bit-shift-io/bike-aid/mcu-attiny-cpp/schematic.kicad_sch

## KiCad design mcu-attiny-cpp/schematic.kicad_sch (2024-03-28)

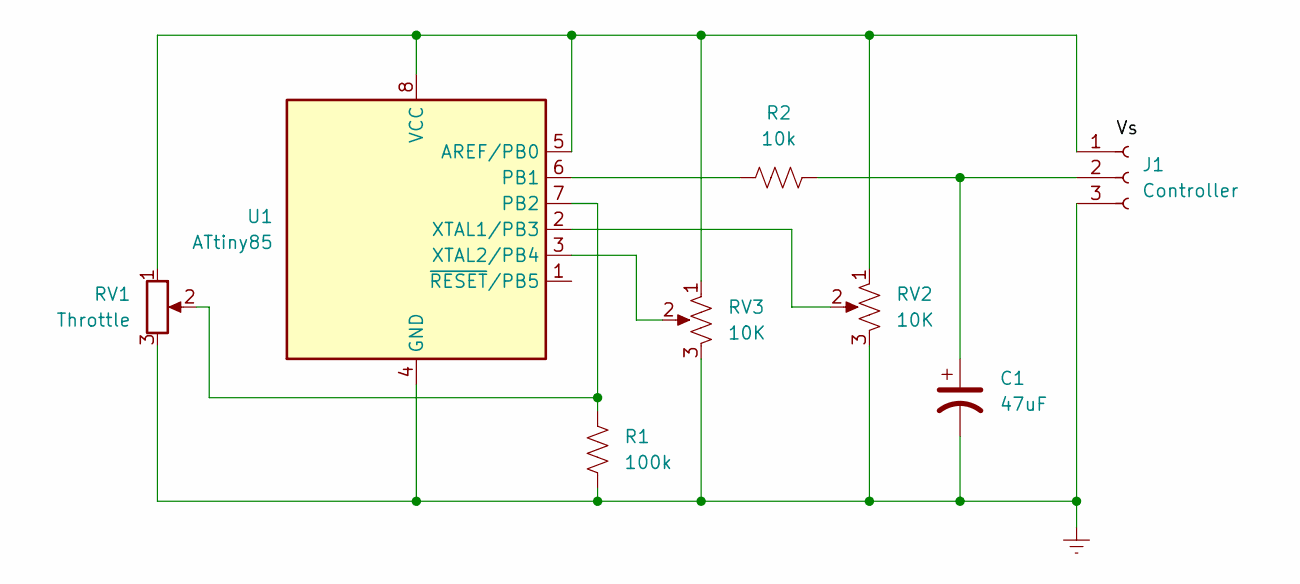
[picture p4: schematic schematic.kicad_sch]

Parts:
C1: 47uF
J1: Controller
R1: 100k
R2: 10k
RV1: Throttle
RV2, RV3: 10K
U1: ATtiny85; DIP-8_W7.62mm

Connections:
Earth: C1.2, J1.3, R1.2, RV1.3, RV2.3, RV3.3, U1.4 (GND)
unnamed: C1.1, J1.2, R2.1
unnamed: J1.1, RV1.1, RV2.1, RV3.1, U1.5 (AREF/PB0), U1.8 (VCC)
unnamed: R1.1, RV1.2, U1.7 (PB2)
unnamed: R2.2, U1.6 (PB1)
unnamed: RV2.2, U1.2 (XTAL1/PB3)
unnamed: RV3.2, U1.3 (XTAL2/PB4)
