bit-shift-io/bike-aid/mcu-esp-cpp/src/main.cpp

/*
  Bike Aid

  This is an ebike tool which does the following:
  - Bluetooth interface
  - Power on/off
  - Lights on/off
  - Battery power meter
  - Alarm system
  - Speedometer
  - Trip Odometer
  - Trip duration
  - Throttle smoothing
  - Throttle limiting / speed limiting
  - Throttle deadband adjustment
  - Temperature

  Bronson Mathews, 2024
*/

/*
Note: if using pins that dont exist the system will crash. Be cautious when setting new classes
*/

#include "Arduino.h"
#include "log.h"
#include "system.h"
#include "store.h"
#include "alarm.h"
#include "clock.h"
#include "throttle.h"
#include "speed.h"
#include "battery.h"
#include "system.h"
#include "power.h"
#include "temperature.h"
#include "bluetooth.h"


void setup() {

  // order important
  Log.init(115200);
  Store.init();
  Bluetooth.init();
  System.init();

  // enable modules
  // testing set true
  Temperature::instance().set_enable(true);
  Alarm::instance().set_enable(true);
  Speed::instance().set_enable(true);
  Throttle::instance().set_enable(false);
  Power::instance().set_enable(true);
  Clock::instance().set_enable(true);

  Log.println("boot ok!");Log.println();
}

void loop() {
  Alarm::instance().update();
  Throttle::instance().update();
  Speed::instance().update();
  Clock::instance().update();
  Temperature::instance().update();
}
