bit-shift-io/bike-aid/mcu-nrf-rs/src/tasks/piezo.rs

use crate::utils::{note::*, melody, signals};
use embassy_nrf::gpio::AnyPin;
use defmt::info;
use embassy_nrf::peripherals::PWM0;
use embassy_nrf::pwm::SimplePwm;
use embassy_time::Timer;

const TASK_ID: &str = "PIEZO";

#[embassy_executor::task]
pub async fn task(
    pwm_device: PWM0,
    pin: AnyPin
) {
    //return; // debug

    info!("{}", TASK_ID);

    let mut pwm = SimplePwm::new_1ch(pwm_device, pin);
    let mut rec_mode = signals::PIEZO_MODE.receiver().unwrap();
    let mut piezo_mode = PiezoMode::None;

    loop {
        // Try to poll read new mode
        // doing this way allows us to use the default mode, if no value is set
        if let Some(b) = rec_mode.try_changed() {piezo_mode = b}

        match piezo_mode {
            PiezoMode::None => {
                pwm.disable();
                piezo_mode = rec_mode.changed().await;
            },
            PiezoMode::Boot => {
                boot(&mut pwm).await;
                piezo_mode = PiezoMode::None;
            }, 
            PiezoMode::PowerOn => {
                power_on(&mut pwm).await;
                piezo_mode = PiezoMode::None;
            },
            PiezoMode::PowerOff => {
                power_off(&mut pwm).await;
                piezo_mode = PiezoMode::None;
            }
            PiezoMode::Warning => {
                warning(&mut pwm).await;
                piezo_mode = PiezoMode::None;
            }
            PiezoMode::Alarm => alarm(&mut pwm).await, // loop
            PiezoMode::SuperMarioBros => {
                play_tune(&mut pwm, melody::SUPER_MARIO_BROS.as_slice(), melody::SUPER_MARIO_BROS_TEMPO).await;
                piezo_mode = PiezoMode::None;
            }
            PiezoMode::Notify => {
                notify(&mut pwm).await;
                piezo_mode = PiezoMode::None;
            },
            PiezoMode::RydeOfTheWalkyries => {
                play_tune(&mut pwm, melody::RYDE_OF_THE_WALKYRIES.as_slice(), melody::RYDE_OF_THE_WALKYRIES_TEMPO).await;
                piezo_mode = PiezoMode::None;
            },
            PiezoMode::BeepShort => {
                beep_short(&mut pwm).await;
                piezo_mode = PiezoMode::None;
            },
            PiezoMode::BeepLong => {
                beep_long(&mut pwm).await;
                piezo_mode = PiezoMode::None;
            },
        };
    }
}


#[allow(dead_code)]
#[derive(Clone,Copy)]
pub enum PiezoMode {
    None,
    Boot,
    PowerOn,
    PowerOff,
    Warning,
    Alarm,
    SuperMarioBros,
    Notify,
    RydeOfTheWalkyries,
    BeepShort,
    BeepLong,
}


async fn beep_short(
    pwm: &mut SimplePwm<'_, PWM0>, // dont need 'static here
) {
    pwm.enable();
    pwm.set_period(NOTE_F6.try_into().unwrap());
    pwm.set_duty(0, pwm.max_duty() / 2); // duty changes with period, so needs to be reset each time
    Timer::after_millis(100).await;
    pwm.disable();
}


async fn beep_long(
    pwm: &mut SimplePwm<'_, PWM0>, // dont need 'static here
) {
    pwm.enable();
    pwm.set_period(NOTE_D3.try_into().unwrap());
    pwm.set_duty(0, pwm.max_duty() / 2); // duty changes with period, so needs to be reset each time
    Timer::after_millis(400).await;
    pwm.disable();
}


async fn notify(
    pwm: &mut SimplePwm<'_, PWM0>, // dont need 'static here
) {
    let tempo: i32 = 120;
    let tune: [isize; 12] = [
        NOTE_C4, 12, NOTE_C5, 12, NOTE_A3, 12, NOTE_A4, 12 ,NOTE_AS3, 12, NOTE_AS4, 12
    ];
    play_tune(pwm, tune.as_slice(), tempo).await;
}


async fn boot(
    pwm: &mut SimplePwm<'_, PWM0>, // dont need 'static here
) {
    play_tune(pwm, melody::STAR_TREK.as_slice(), melody::STAR_TREK_TEMPO).await;
}


async fn power_on(
    pwm: &mut SimplePwm<'_, PWM0>, // dont need 'static here
) {
    play_tune(pwm, melody::NOKIA.as_slice(), melody::NOKIA_TEMPO).await;
}


async fn power_off(
    pwm: &mut SimplePwm<'_, PWM0>, // dont need 'static here
) {
    play_tune(pwm, melody::NOKIA.as_slice(), melody::NOKIA_TEMPO).await;
}


async fn alarm(
    pwm: &mut SimplePwm<'_, PWM0>, // dont need 'static here
) {
    play_tune(pwm, melody::PACMAN.as_slice(), melody::PACMAN_TEMPO).await;
}


async fn warning(
    pwm: &mut SimplePwm<'_, PWM0>,
) {
    play_tune(pwm, melody::STAR_TREK.as_slice(), melody::STAR_TREK_TEMPO).await;
}


async fn play_tune(
    pwm: &mut SimplePwm<'_, PWM0>, 
    tune: &[isize], 
    tempo: i32
) {
    let length = tune.len() / 2;
    let wholenote = (60000.0 * 4.0) / tempo as f32; // wholenote (ms) = 60,000 (1 minute in ms) * 4 (length of whole note) / tempo (bpm)
    let duty = pwm.max_duty() / 2; // piezo driver suggests 50% of max duty


    // loop over each note,duration combo
    for n in (0..=length).step_by(2) {

        // calculates the duration of each note
        let mut duration: f32 = 0.0;
        let divider = tune[n + 1] as i16; // can be negative
        if divider > 0 {
            // regular note, just proceed
            duration = wholenote / divider as f32;
        } else if divider < 0 {
            // dotted notes are represented with negative durations!!
            duration = wholenote / divider.abs() as f32;
            duration *= 1.5 as f32; // increases the duration in half for dotted notes
        }
        let note_duration = (duration * 0.9) as u64;
        let delay_duration = (duration * 0.1) as u64;

        // get the note value
        let note_val = tune[n].try_into().unwrap();
        if note_val != 0 { // 0 is a rest, so no tune
            pwm.enable();
            pwm.set_period(note_val); // TODO: try 16_000_000 / tone.1
            pwm.set_duty(0, duty); // duty changes with period, so needs to be reset each time
        }

        // Wait for the specief duration before playing the next note.
        // we only play the note for 90% of the duration, leaving 10% as a pause
        Timer::after_millis(note_duration).await;

        // stop the waveform generation before the next note.
        pwm.disable();
        Timer::after_millis(delay_duration).await;
    }
}
