bit-shift-io/bike-aid/mcu-nrf-rs/src/tasks/cruise.rs

use core::future;

use crate::utils::{settings, signals};
use defmt::info;
use embassy_futures::select::{select, select3, Either3};
use embassy_time::Instant;

const TASK_ID: &str = "CRUISE";
const NO_THROTTLE_THRESHOLD: u16 = 1200;
const FULL_THROTTLE_THRESHOLD: u16 = 2600;
const BRAKE_TAP_TIME: u64 = 300; // ms
const THROTTLE_MAX_COUNT: u8 = 8; // this equals X x 100ms of throttle updates

#[embassy_executor::task]
pub async fn task() {
    info!("{}", TASK_ID);

    // power on/off
    let mut rec_power_on = signals::POWER_ON.receiver().unwrap();
    let mut state_power_on = rec_power_on.try_get().unwrap();

    // sport mode - cruise enabled/disabled
    let mut rec_sport_mode_on = signals::SPORT_MODE_ON.receiver().unwrap();
    let mut state_sport_mode_on = rec_sport_mode_on.try_get().unwrap();

    loop {
        match select3(rec_power_on.changed(), rec_sport_mode_on.changed(), run(state_power_on, state_sport_mode_on)).await {
            Either3::First(b) => { state_power_on = b; },
            Either3::Second(b) => { state_sport_mode_on = b; },
            Either3::Third(_) => {}
        }
    }
}


async fn run(power_on: bool, sport_mode_on: bool) {
    // power off/sport mode
    // throttle and brake dont work when power off
    // but we need to reset it when powered off purely for gui
    if !power_on || sport_mode_on {
        set_cruise(0).await; 
        future::pending().await // wait/yield forever doing nothing
    }

    // throttle and brake tap detection
    select(throttle_tap(), brake_tap()).await;
}

async fn brake_tap() {
    let mut rec_brake_on = signals::BRAKE_ON.receiver().unwrap();

     // wait for brake off - not sure if this is needed?
     //rec_brake_on.changed_and(|b| *b == false).await;

    loop {
        // brake should be off here from boot & previous loop
        // wait for brake on
        rec_brake_on.changed_and(|b| *b == true).await;

        // start timing
        let time = Instant::now();

        // wait for brake off
        rec_brake_on.changed_and(|b| *b == false).await;

        if delta(time) < BRAKE_TAP_TIME {
            //info!("brake tap");
            decrement_cruise().await;
        } else {
            // regaulr brake, so reset cruise
            set_cruise(0).await;
        }
    }
}


async fn throttle_tap() {
    let mut rec_throttle = signals::THROTTLE_IN.receiver().unwrap();
    let mut throttle_voltage = rec_throttle.changed().await; // millivolts, initial value

    loop {
        // Wait for throttle to go below the NO_THROTTLE_THRESHOLD - throttle off
        while throttle_voltage > NO_THROTTLE_THRESHOLD {
            throttle_voltage = rec_throttle.changed().await;
        }

        // Wait for the throttle to exceed the NO_THROTTLE_THRESHOLD - throttle start/low
        while throttle_voltage < NO_THROTTLE_THRESHOLD {
            throttle_voltage = rec_throttle.changed().await;
        }

        // start timing, each update is 100ms
        let mut count = 0;

        // Wait for the throttle to exceed the FULL_THROTTLE_THRESHOLD - throttle high
        while throttle_voltage < FULL_THROTTLE_THRESHOLD && count < THROTTLE_MAX_COUNT {
            throttle_voltage = rec_throttle.changed().await;
            count += 1;
        }

        // Now we are at full throttle, wait for it to drop below the NO_THROTTLE_THRESHOLD - throttle off
        while throttle_voltage > NO_THROTTLE_THRESHOLD && count < THROTTLE_MAX_COUNT {
            throttle_voltage = rec_throttle.changed().await;
            count += 1;
        }

        // Check if the tap was detected within the time limit
        if count < THROTTLE_MAX_COUNT {
            //info!("tap detected");
            increment_cruise().await;
        }
    }
}


pub fn delta(t: Instant) -> u64 {
    Instant::now().duration_since(t).as_millis()
}


async fn increment_cruise() {
    let mut level = signals::CRUISE_LEVEL.try_get().unwrap();
    if level == 5 { return; }

    level += 1;
    // wrap around 0-4, move 0 -> 5 = range 1-5 instead of 0-4
    //level = (level + 1) % 5; 
    //if level == 0 { level = 5; }

    set_cruise(level).await;
}


async fn decrement_cruise() {
    let mut level = signals::CRUISE_LEVEL.try_get().unwrap();
    if level == 0 { return; }

    level -= 1;
    // wrap around 0-4, move 5 -> 0 = range 1-5 instead of 0-4
    //level = (level - 1) % 5;
    //if level == 0 { level = 5; }

    set_cruise(level).await;
}


async fn set_cruise(level: u8) {
    let current_level = signals::CRUISE_LEVEL.try_get().unwrap();

    // only send if changed
    if current_level != level {
        // set voltage
        let cruise_voltages = *settings::CRUISE_VOLTAGES.lock().await;
        let voltage = if level == 0 { 0 } else { cruise_voltages[(level -1) as usize] }; 
        settings::CRUISE_VOLTAGE.dyn_sender().send(voltage);

        // set level
        signals::CRUISE_LEVEL.dyn_sender().send(level);
        signals::send_ble(signals::BleHandles::CruiseLevel, &[level]);
    
        // beep
        let send_piezo = signals::PIEZO_MODE.sender();
        send_piezo.send(signals::PiezoModeType::BeepShort);
    }
}
