bit-shift-io/bike-aid/mcu-nrf-rs/src/tasks/bluetooth.rs

use crate::ble::server::{self, Server};
use defmt::*;
use embassy_executor::Spawner;
use embassy_futures::select::select;
use core::mem;
use nrf_softdevice::ble::advertisement_builder::{Flag, LegacyAdvertisementBuilder, LegacyAdvertisementPayload, ServiceList};
use nrf_softdevice::ble::{self, gatt_server, peripheral, Connection};
use nrf_softdevice::{raw, Softdevice};
use core::pin::pin;

const TASK_ID: &str = "BLUETOOTH";

// main task
#[embassy_executor::task]
pub async fn task(
    spawner: Spawner
) {
    info!("{}", TASK_ID);
    
    // start softdevice with fixed address
    let softdevice = Softdevice::enable(&get_config());
    let address = ble::Address::new(ble::AddressType::Public, [0x45, 0x42, 0x60, 0xFB, 0xEB, 0xD7]);
    ble::set_address(softdevice, &address);
    let server: Server = unwrap!(Server::new(softdevice));
    spawner.must_spawn(softdevice_task(softdevice));
   
    // advertise and scan data
    static ADV_DATA: LegacyAdvertisementPayload = LegacyAdvertisementBuilder::new()
        .flags(&[Flag::GeneralDiscovery, Flag::LE_Only])
        //.services_16(ServiceList::Incomplete, &[ServiceUuid16::from_u16(0xFE2C)]) // fast pair
        .short_name("BScooter")
        .build();

    static SCAN_DATA: LegacyAdvertisementPayload = LegacyAdvertisementBuilder::new()
        //.services_16(ServiceList::Incomplete, &[ServiceUuid16::from_u16(0xFE2C)]) // fast pair
        .services_128(ServiceList::Incomplete, &[[0x9E, 0xCA, 0xDC, 0x24, 0x0E, 0xE5, 0xA9, 0xE0, 0x93, 0xF3, 0xA3, 0xB5, 0x01, 0x00, 0x40, 0x6E]]) // UART Service
        .build();

    // start the show
    loop {
        let config = peripheral::Config::default();
        let advertisement = peripheral::ConnectableAdvertisement::ScannableUndirected { adv_data: &ADV_DATA, scan_data: &SCAN_DATA };
        let connection: Connection = unwrap!(peripheral::advertise_connectable(softdevice, advertisement, &config).await);

        // Create two futures. Pin locks the memory to the stack
        let server_future = pin!(server::run(&connection, &server));
        let gatt_future = pin!(gatt_server::run(&connection, &server, |_| {})); // no events rigistered

        //  - we only gather data when a client is connected, therefore saving some power.
        //  - when the GATT server finishes operating, our run function does also
        select(server_future, gatt_future).await;

        // disconnect message
        server::disconnected(&connection, &server).await;
    }
}


fn get_config() -> nrf_softdevice::Config {
    nrf_softdevice::Config {
        clock: Some(raw::nrf_clock_lf_cfg_t {
            source: raw::NRF_CLOCK_LF_SRC_RC as u8,
            rc_ctiv: 16,
            rc_temp_ctiv: 2,
            accuracy: raw::NRF_CLOCK_LF_ACCURACY_500_PPM as u8,
        }),
        conn_gap: Some(raw::ble_gap_conn_cfg_t {
            conn_count: 2, // 6
            event_length: 24, // 24
        }),
        conn_gatt: Some(raw::ble_gatt_conn_cfg_t { att_mtu: 517 }), // 517 is the android default
        gatts_attr_tab_size: Some(raw::ble_gatts_cfg_attr_tab_size_t { attr_tab_size: 2048 }), // increase if nomem error, default: attr_tab_size: raw::BLE_GATTS_ATTR_TAB_SIZE_DEFAULT,
        gap_role_count: Some(raw::ble_gap_cfg_role_count_t {
            adv_set_count: 1,
            periph_role_count: 1, // 3
            central_role_count: 1, // 3
            central_sec_count: 0,
            _bitfield_1: raw::ble_gap_cfg_role_count_t::new_bitfield_1(0),
        }),
        gap_device_name: Some(raw::ble_gap_cfg_device_name_t {
            p_value: b"BScooter" as *const u8 as _, // TODO: use device name here
            current_len: 8,
            max_len: 8,
            write_perm: unsafe { mem::zeroed() },
            _bitfield_1: raw::ble_gap_cfg_device_name_t::new_bitfield_1(raw::BLE_GATTS_VLOC_STACK as u8),
        }),
        ..Default::default()
    }
}


// softdevice task
#[embassy_executor::task]
async fn softdevice_task(sd: &'static Softdevice) {
    sd.run().await;
}
