bit-shift-io/bike-aid/mcu-nrf-rs/src/tasks/clock.rs

use crate::utils::signals;
use embassy_futures::select::select;
use embassy_time::{Instant, Timer};
use defmt::info;

const TASK_ID: &str = "CLOCK";

#[embassy_executor::task]
pub async fn task() {
    info!("{}", TASK_ID);

    // power on/off
    let mut rec_power_on = signals::POWER_ON.receiver().unwrap();

    loop { 
        if rec_power_on.changed().await {
            select(rec_power_on.changed(), clock()).await;
        }
    }
}


async fn clock() {
    let mut last_minutes: u8 = 0;
    let mut last_hours: u8 = 0;
    let start_time = Instant::now();

    // send/reset initial time
    signals::send_ble(signals::BleHandles::ClockMinutes, &[0]);
    signals::send_ble(signals::BleHandles::ClockHours, &[0]);
    
    loop {
        Timer::after_secs(60).await;

        let seconds = start_time.elapsed().as_secs();
        let hours = ((seconds % 86400) / 3600) as u8; // 3600 seconds in an hour
        let minutes = ((seconds % 3600) / 60) as u8; // 60 seconds in a minute

        if minutes != last_minutes {
            last_minutes = minutes;
            signals::send_ble(signals::BleHandles::ClockMinutes, &[minutes]);
        };
    
        if hours != last_hours {
            last_hours = hours;
            signals::send_ble(signals::BleHandles::ClockHours, &[hours]);
        }
    }
}
