bit-shift-io/bike-aid/mcu-nrf-rs/src/tasks/mod.rs

pub mod alarm;
pub mod battery_adc;
pub mod battery;
pub mod bluetooth;
pub mod brake;
pub mod cli;
pub mod clock;
pub mod cruise;
pub mod gyroscope;
pub mod led;
pub mod manual_override;
pub mod park_brake;
pub mod piezo;
pub mod power_down;
pub mod rtt;
pub mod speed;
pub mod switch_power;
pub mod temperature;
pub mod throttle_adc;
pub mod throttle_dac;
pub mod throttle;
