bit-shift-io/bike-aid/mcu-esp-cpp/include/bluetooth.h

// handy guide https://github.com/nkolban/ESP32_BLE_Arduino/blob/master/examples/BLE_uart/BLE_uart.ino

#pragma once
#include "NimBLEDevice.h"


class BluetoothClass {

  public:
    BluetoothClass();
    void init();

    void set_value(BLECharacteristic *pCharacteristic, std::string value);
    void set_value(BLECharacteristic *pCharacteristic, uint8_t value);

    // callbacks
    void on_connect(BLEServer* pServer);
    void on_disconnect(BLEServer* pServer);
    void on_write(BLECharacteristic *pCharacteristic);


    // services

    // characteristics
    BLECharacteristic *power_system_characteristic;
    BLECharacteristic *power_lights_characteristic;
    BLECharacteristic *alarm_enabled_characteristic;
    BLECharacteristic *battery_level_characteristic;
    BLECharacteristic *throttle_smoothing_characteristic;
    BLECharacteristic *temperature_characteristic;
    BLECharacteristic *trip_distance_characteristic;
    BLECharacteristic *trip_duration_characteristic;
    BLECharacteristic *speed_characteristic;

    // uart
    BLECharacteristic *uart_tx_characteristic;
    BLECharacteristic *uart_rx_characteristic;

  private:
    // https://www.uuidgenerator.net/
    const char* SERVICE_UUID = "8fabcc8a-0a6e-4c37-b640-eb5adf88b465";
    const char* THROTTLE_SMOOTHING_UUID = "beb5483e-36e1-0000-b7f5-ea07361b26a8";
    const char* ALARM_ENABLED_UUID = "beb5483e-36e1-0001-b7f5-ea07361b26a8";
    const char* POWER_SYSTEM_UUID = "beb5483e-36e1-0002-b7f5-ea07361b26a8";
    const char* POWER_LIGHTS_UUID = "beb5483e-36e1-0003-b7f5-ea07361b26a8";

    const int PIN_CODE = 123456;

    // UART service UUID
    // https://learn.adafruit.com/introducing-adafruit-ble-BluetoothClass-low-energy-friend/uart-service
    const char* SERVICE_UART_UUID =       "6E400001-B5A3-F393-E0A9-E50E24DCCA9E"; 
    const char* CHARACTERISTIC_RX_UUID =  "6E400002-B5A3-F393-E0A9-E50E24DCCA9E"; // tx??
    const char* CHARACTERISTIC_TX_UUID =  "6E400003-B5A3-F393-E0A9-E50E24DCCA9E"; // rx id??

    // server
    BLEServer *pServer = NULL;



    // callbacks
    bool device_connected = false;
    bool old_device_connected = false;

    // Delay between loops in ms
    const int INTERVAL = 6000; // 1 minute
    unsigned long last_interval = 0;
};

extern BluetoothClass Bluetooth;
