bit-shift-io/bike-aid/mcu-esp-cpp/include/system.h

#pragma once

// guide 
// https://mischianti.org/esp32-practical-power-saving-manage-wifi-and-cpu-1/

class SystemClass {
  
  public:
    SystemClass();
    void init();
    void set_power_low();
    void set_power_high();
    void print_cpu_info();
    void update();
};

extern SystemClass System;
