bit-shift-io/bike-aid/mcu-esp-cpp/src/system.cpp

#include "system.h"
#include <WiFi.h>
#include <esp_wifi.h>
#include "driver/adc.h"
#include <esp_task_wdt.h>
#include "esp32-hal.h"
#include "log.h"

SystemClass System;


SystemClass::SystemClass() {
}


void SystemClass::init() {
  Log.println("SystemClass init");
  print_cpu_info();
  //set_power_low(); // crash!
}


void SystemClass::print_cpu_info() {
  Log.println("-------------");
  Log.print("CPU Freq = ");
  Log.print(getCpuFrequencyMhz());
  Log.println(" MHz");

  Log.print("XTAL Freq = ");
  Log.print(getXtalFrequencyMhz());
  Log.println(" MHz");

  Log.print("APB Freq = ");
  Log.print(getApbFrequency());
  Log.println(" Hz");
  Log.println("-------------");
}


void SystemClass::set_power_low() {
  // wifi power mode
  //esp_wifi_set_ps(WIFI_PS_MAX_MODEM); // lowest
  //esp_wifi_set_ps(WIFI_PS_MIN_MODEM); // low

  // disable adc and wifi
  adc_power_off();
  WiFi.disconnect(true);  // Disconnect from the network
  WiFi.mode(WIFI_OFF);    // Switch WiFi off

  // bluetooth off
  //btStop();

  // cpu freq, bluetooth needs 80mhz or above
  //  240, 160, 80    <<< For all XTAL types
  //  40, 20, 10      <<< For 40MHz XTAL
  //  26, 13          <<< For 26MHz XTAL
  //  24, 12          <<< For 24MHz XTAL
  setCpuFrequencyMhz(80);

  // disable watch dog when using less than 80mhz
  //disableCore0WDT();
}


void SystemClass::set_power_high() {
  // wifi power mode
  esp_wifi_set_ps(WIFI_PS_NONE); // default

  // enable adc and wifi
  adc_power_on(); delay(200);
  WiFi.disconnect(false);  // Reconnect the network
  WiFi.mode(WIFI_STA);    // Switch WiFi off

  // bluetooth on
  btStart();

  // cpu freq
  setCpuFrequencyMhz(240);
}
