bit-shift-io/bike-aid/mcu-nrf-rs/src/utils/note.rs

#![allow(dead_code)]

// note frequency chart https://muted.io/note-frequencies/
// needs to be isize(not usize) because durations can be negative

pub const REST: isize = 0;
pub const NOTE_C0: isize = 16;
pub const NOTE_CS0: isize = 17;
pub const NOTE_D0: isize = 19;
pub const NOTE_DS0: isize = 21;
pub const NOTE_E0: isize = 22;
pub const NOTE_F0: isize = 24;
pub const NOTE_FS0: isize = 26;
pub const NOTE_G0: isize = 28;
pub const NOTE_GS0: isize = 29;
pub const NOTE_A0: isize = 30;
pub const NOTE_B0: isize = 31;
pub const NOTE_C1: isize = 33;
pub const NOTE_CS1: isize = 35;
pub const NOTE_D1: isize = 37;
pub const NOTE_DS1: isize = 39;
pub const NOTE_E1: isize = 41;
pub const NOTE_F1: isize = 44;
pub const NOTE_FS1: isize = 46;
pub const NOTE_G1: isize = 49;
pub const NOTE_GS1: isize = 52;
pub const NOTE_A1: isize = 55;
pub const NOTE_AS1: isize = 58;
pub const NOTE_B1: isize = 62;
pub const NOTE_C2: isize = 65;
pub const NOTE_CS2: isize = 69;
pub const NOTE_D2: isize = 73;
pub const NOTE_DS2: isize = 78;
pub const NOTE_E2: isize = 82;
pub const NOTE_F2: isize = 87;
pub const NOTE_FS2: isize = 93;
pub const NOTE_G2: isize = 98;
pub const NOTE_GS2: isize = 104;
pub const NOTE_A2: isize = 110;
pub const NOTE_AS2: isize = 117;
pub const NOTE_B2: isize = 123;
pub const NOTE_C3: isize = 131;
pub const NOTE_CS3: isize = 139;
pub const NOTE_D3: isize = 147;
pub const NOTE_DS3: isize = 156;
pub const NOTE_E3: isize = 165;
pub const NOTE_F3: isize = 175;
pub const NOTE_FS3: isize = 185;
pub const NOTE_G3: isize = 196;
pub const NOTE_GS3: isize = 208;
pub const NOTE_A3: isize = 220;
pub const NOTE_AS3: isize = 233;
pub const NOTE_B3: isize = 247;
pub const NOTE_C4: isize = 262;
pub const NOTE_CS4: isize = 277;
pub const NOTE_D4: isize = 294;
pub const NOTE_DS4: isize = 311;
pub const NOTE_E4: isize = 330;
pub const NOTE_F4: isize = 349;
pub const NOTE_FS4: isize = 370;
pub const NOTE_G4: isize = 392;
pub const NOTE_GS4: isize = 415;
pub const NOTE_A4: isize = 440;
pub const NOTE_AS4: isize = 466;
pub const NOTE_B4: isize = 494;
pub const NOTE_C5: isize = 523;
pub const NOTE_CS5: isize = 554;
pub const NOTE_D5: isize = 587;
pub const NOTE_DS5: isize = 622;
pub const NOTE_E5: isize = 659;
pub const NOTE_F5: isize = 698;
pub const NOTE_FS5: isize = 740;
pub const NOTE_G5: isize = 784;
pub const NOTE_GS5: isize = 831;
pub const NOTE_A5: isize = 880;
pub const NOTE_AS5: isize = 932;
pub const NOTE_B5: isize = 988;
pub const NOTE_C6: isize = 1047;
pub const NOTE_CS6: isize = 1109;
pub const NOTE_D6: isize = 1175;
pub const NOTE_DS6: isize = 1245;
pub const NOTE_E6: isize = 1319;
pub const NOTE_F6: isize = 1397;
pub const NOTE_FS6: isize = 1480;
pub const NOTE_G6: isize = 1568;
pub const NOTE_GS6: isize = 1661;
pub const NOTE_A6: isize = 1760;
pub const NOTE_AS6: isize = 1865;
pub const NOTE_B6: isize = 1976;
pub const NOTE_C7: isize = 2093;
pub const NOTE_CS7: isize = 2217;
pub const NOTE_D7: isize = 2349;
pub const NOTE_DS7: isize = 2489;
pub const NOTE_E7: isize = 2637;
pub const NOTE_F7: isize = 2794;
pub const NOTE_FS7: isize = 2960;
pub const NOTE_G7: isize = 3136;
pub const NOTE_GS7: isize = 3322;
pub const NOTE_A7: isize = 3520;
pub const NOTE_AS7: isize = 3729;
pub const NOTE_B7: isize = 3951;
pub const NOTE_C8: isize = 4186;
pub const NOTE_CS8: isize = 4435;
pub const NOTE_D8: isize = 4699;
pub const NOTE_DS8: isize = 4978;
pub const NOTE_E8: isize = 5274;
pub const NOTE_F8: isize = 5587;
pub const NOTE_FS8: isize = 5919;
pub const NOTE_G8: isize = 6271;
pub const NOTE_GS8: isize = 6643;
pub const NOTE_A8: isize = 7040;
pub const NOTE_AS8: isize = 7459;
pub const NOTE_B8: isize = 7902;
