bit-shift-io/bike-aid/mcu-nrf-rs/src/utils/mod.rs

pub mod data_slice;
pub mod functions;
pub mod globals;
//pub mod log;
pub mod i2c;
//pub mod macros;
pub mod melody;
pub mod note;
pub mod panic_handler;
pub mod profile;
pub mod settings;
pub mod signals;
