bit-shift-io/bike-aid/mcu-nrf-rs/src/examples/blinky.rs

use embassy_time::Timer;
use defmt::info;
use embassy_nrf::gpio::{AnyPin, Level, Output, OutputDrive};

const TASK_ID: &str = "BLINKY";

#[embassy_executor::task]
pub async fn task (
    pin: AnyPin
) {
    info!("{}", TASK_ID);
    let mut led = Output::new(pin, Level::Low, OutputDrive::Standard);

    loop { 
        led.set_high();
        Timer::after_millis(1000).await;
        led.set_low();
        Timer::after_millis(1000).await;
    };
}
