bit-shift-io/bike-aid/mcu-nrf-rs/src/examples/temperature.rs

use crate::utils::signals;
use embassy_nrf::{peripherals::TEMP, temp::Temp};
use embassy_time::Timer;
use embassy_nrf::{bind_interrupts, interrupt};
use embassy_nrf::interrupt::InterruptExt;
use embassy_nrf::temp;
use defmt::info;

const TASK_ID: &str = "TEMPERATURE";

#[embassy_executor::task]
pub async fn temperature (
    temp: TEMP
) {
    info!("{}", TASK_ID);
    /*
    // NOTE: This crashes when using the softdevice!
    // this is an example only for use without the softdevice
    
    bind_interrupts!(struct Irqs {TEMP => temp::InterruptHandler;});
    interrupt::TEMP.set_priority(interrupt::Priority::P3);
    let mut t = Temp::new(temp, Irqs);
    let send_temperature = signals::TEMPERATURE.sender();

    loop {
        let value: u16 = t.read().await.to_num::<u16>();
        //info!("{}", value);
        send_temperature.send(value as u8); // in degrees C, no decimals
        Timer::after_secs(60).await;
    }
     */
}
